yaronski/counterculture/images/IMG_1959.jpg

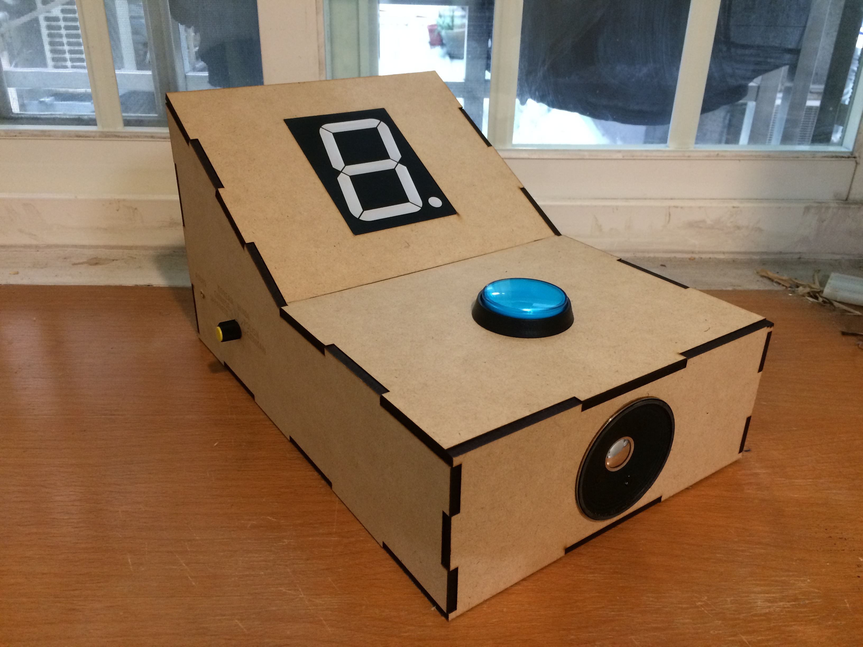
images/IMG_1959.jpg
