yaronski/counterculture/images/IMG_1968.jpg

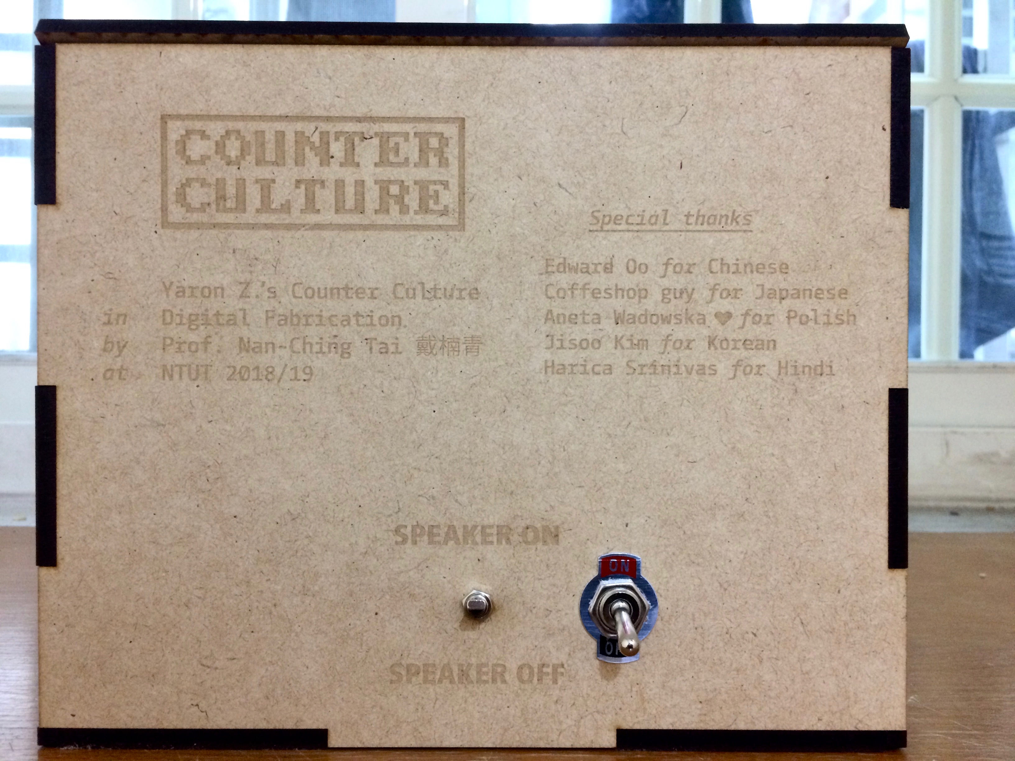
images/IMG_1968.jpg
