yaronski/counterculture/images/IMG_1974 2.jpg

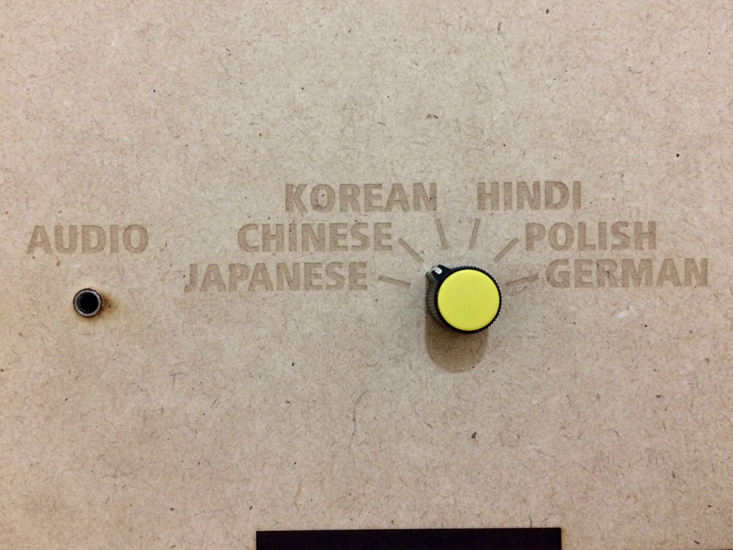
images/IMG_1974 2.jpg
