yaronski/counterculture/images/IMG_1976 2.jpg

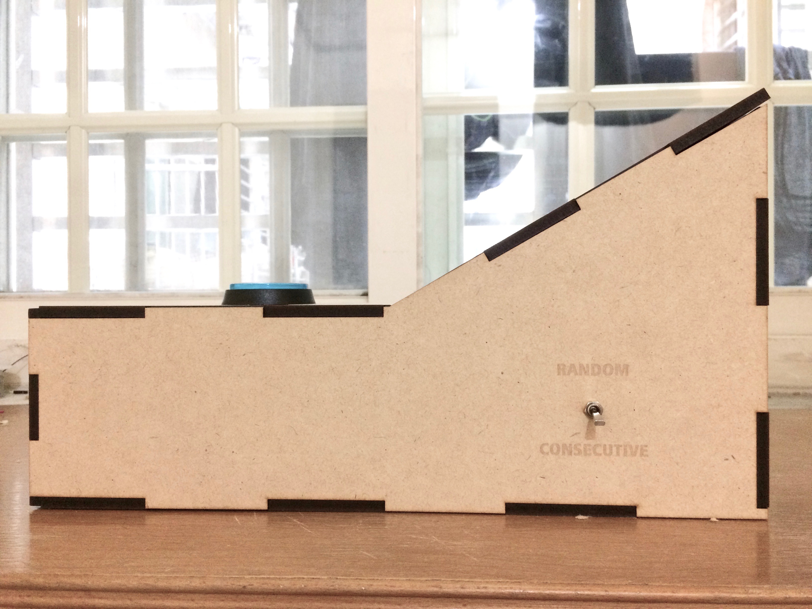
images/IMG_1976 2.jpg
