yaronski/counterculture/images/IMG_1978.jpg

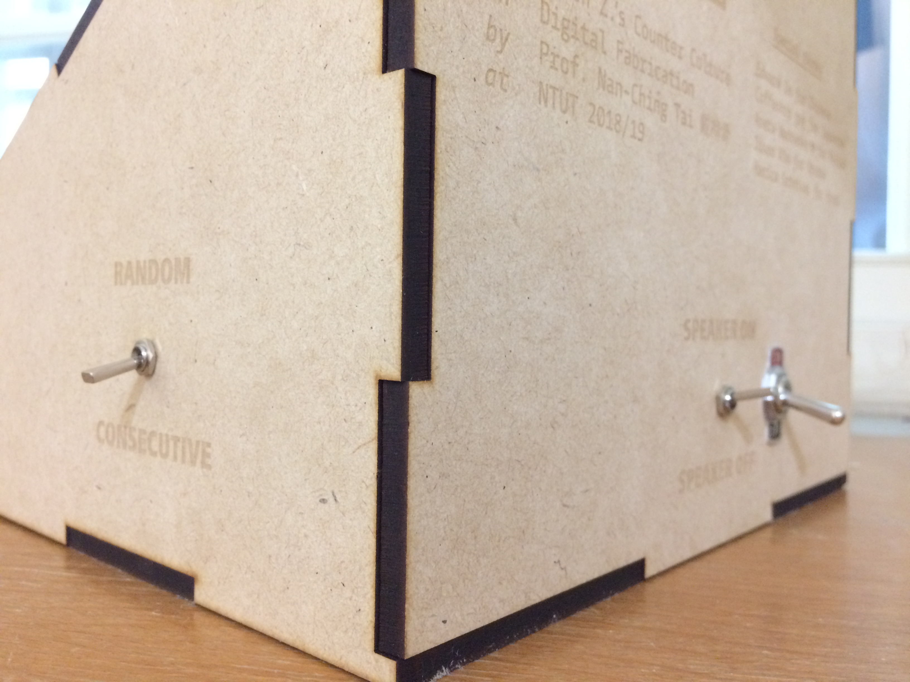
images/IMG_1978.jpg
