yaronski/counterculture/images/IMG_1991.jpg

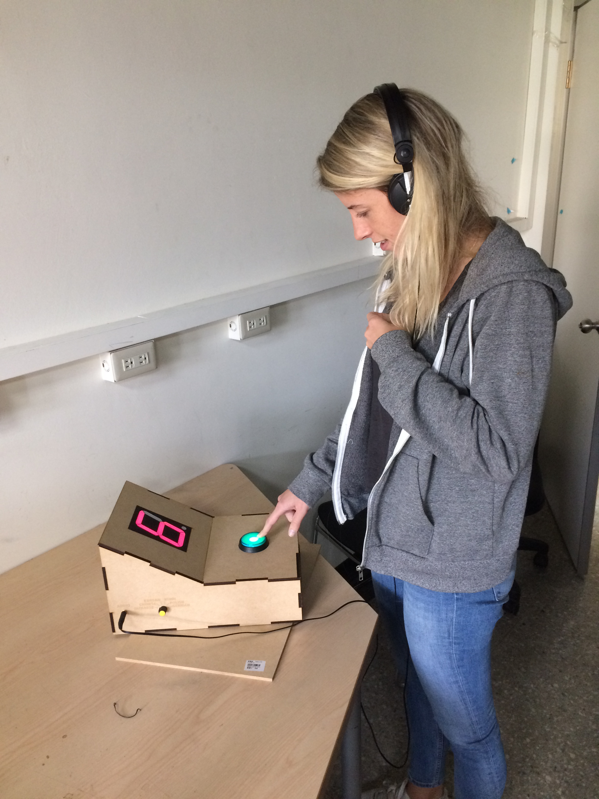
images/IMG_1991.jpg
