yaronski/counterculture/images/IMG_1992.jpg

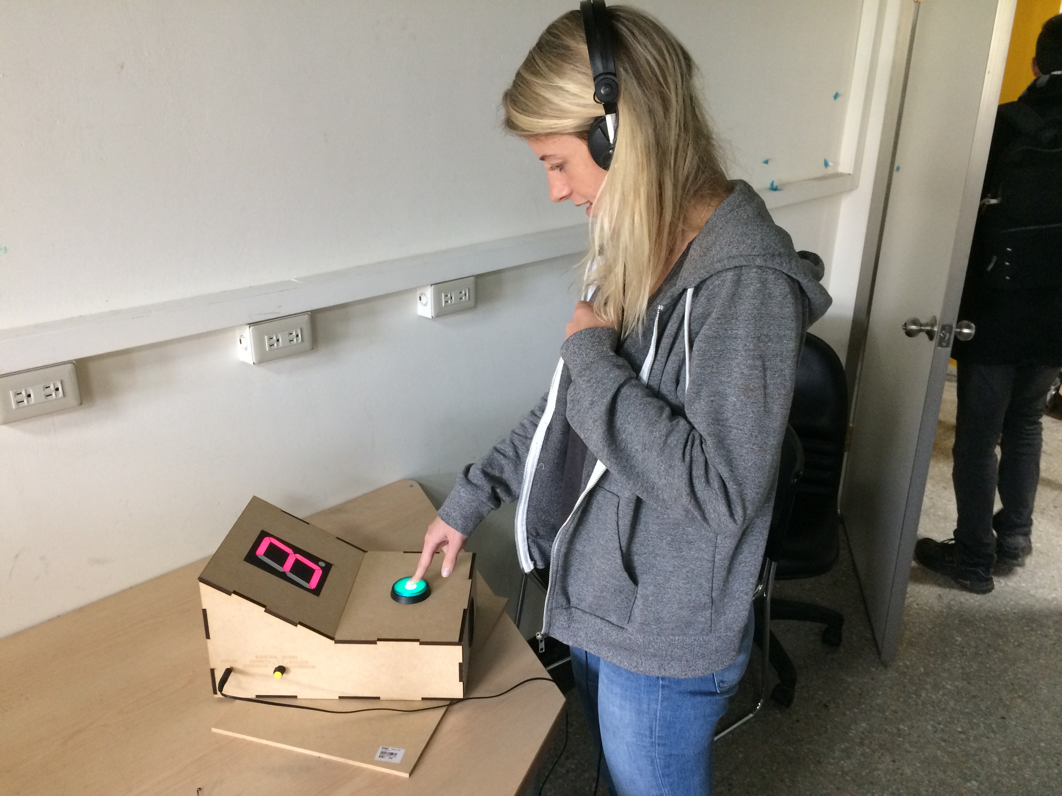
images/IMG_1992.jpg
